ve3sjk/Cyclone-PCB-Factory/Output_files/1212m4/dev pics/2014-12-06 12.56.31.jpg

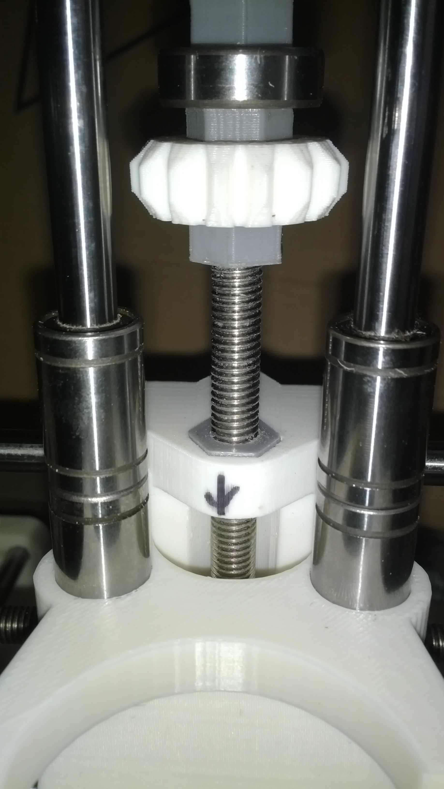
Output_files/1212m4/dev pics/2014-12-06 12.56.31.jpg
