ve3sjk/Cyclone-PCB-Factory/Output_files/1212m4/dev pics/2014-12-06 17.03.23.jpg

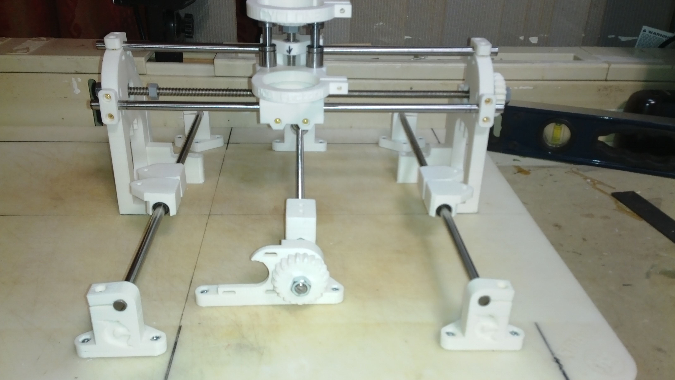
Output_files/1212m4/dev pics/2014-12-06 17.03.23.jpg
