ve3sjk/Cyclone-PCB-Factory/Output_files/ShorterVersion/Cyclone_XrightFrame.stl

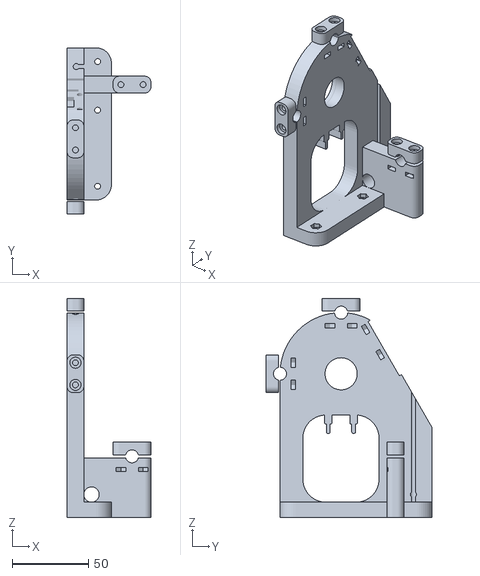
[picture p36: CAD file, 2014-12-10]
Output_files/ShorterVersion/Cyclone_XrightFrame.stl
54.9 x 108.8 x 143.2
