ve3sjk/Cyclone-PCB-Factory/Output_files/templates/Cyclone_workbed_template.dxf

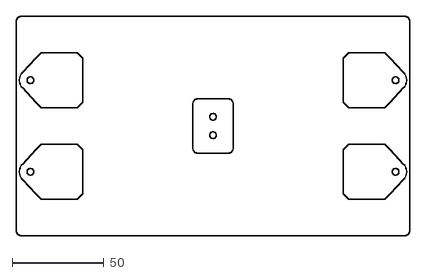
[picture p37: CAD file, 2014-12-10]
Output_files/templates/Cyclone_workbed_template.dxf
215.0 x 120.0
