ve3sjk/Cyclone-PCB-Factory/Output_files/templates/laserCut/Cyclone_workbed_8mm.dxf

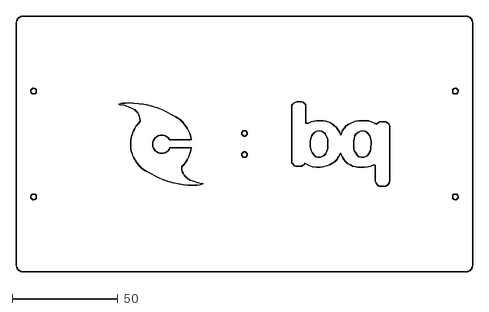
[picture p38: CAD file, 2014-12-10]
Output_files/templates/laserCut/Cyclone_workbed_8mm.dxf
216.0 x 121.0
