ve3sjk/Cyclone-PCB-Factory/Source_files/dxf/oshw.dxf

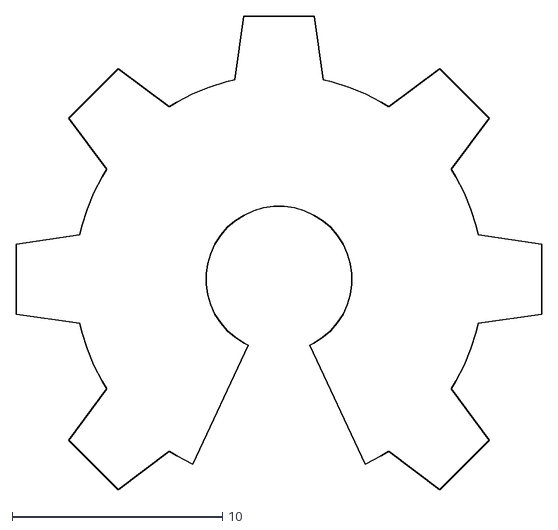
[picture p39: CAD file, 2014-12-10]
Source_files/dxf/oshw.dxf
25.0 x 22.5
