ve3sjk/Cyclone-PCB-Factory/Output_files/1212m4/stl/yleftidler.stl

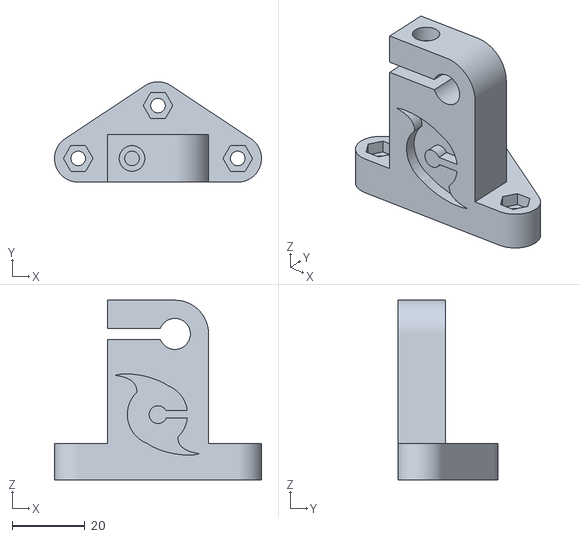
[picture p40: CAD file, 2014-12-08]
Output_files/1212m4/stl/yleftidler.stl
56.8 x 27.5 x 49.2
