ve3sjk/Cyclone-PCB-Factory/Output_files/1212m4/Tool Mounts/Dremel XPR-400 Mount/stl/btm.stl

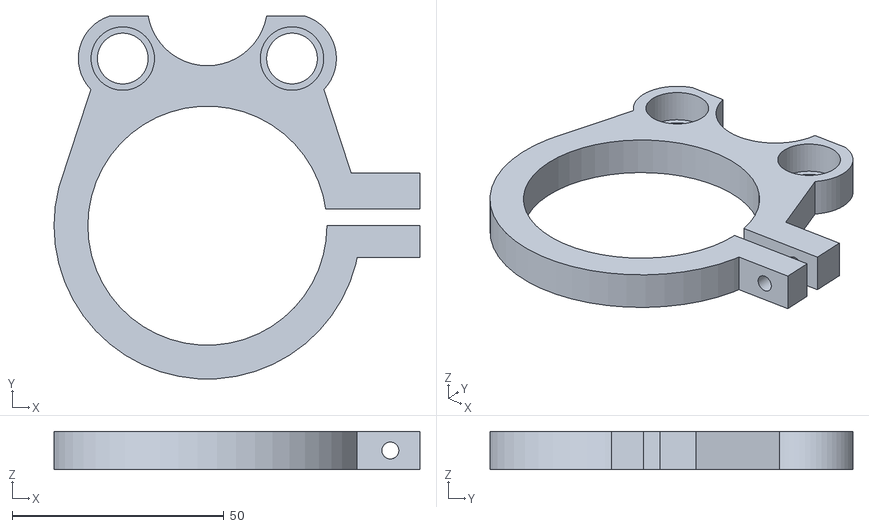
[picture p41: CAD file, 2014-12-08]
Output_files/1212m4/Tool Mounts/Dremel XPR-400 Mount/stl/btm.stl
86.5 x 85.7 x 9.00
