ve3sjk/Cyclone-PCB-Factory/Output_files/Cycl_YbackFrame.stl

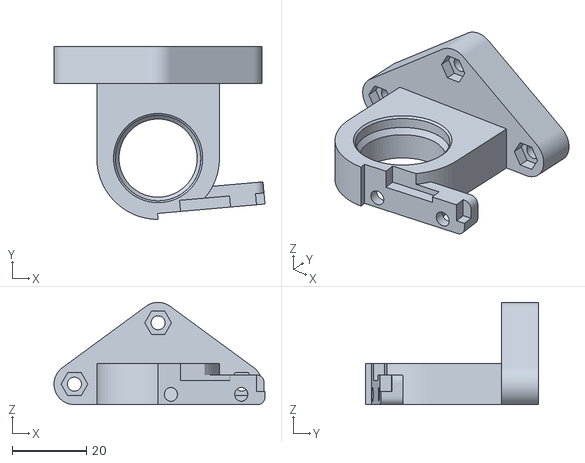
[picture p42: CAD file, 2014-12-10]
Output_files/Cycl_YbackFrame.stl
56.7 x 46.5 x 27.5
