ve3sjk/Cyclone-PCB-Factory/Output_files/templates/laserCut/Electrodo_Calibracion_Cyclone.dxf

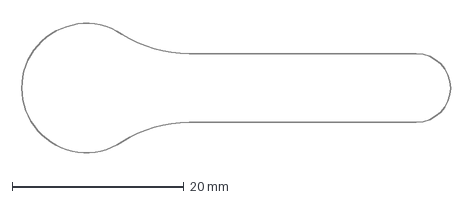
[picture p43: CAD file, 2014-12-10]
Output_files/templates/laserCut/Electrodo_Calibracion_Cyclone.dxf
50.6 x 16.7 mm
