ve3sjk/Cyclone-PCB-Factory/Output_files/1212m4/stl/ygearrod.stl

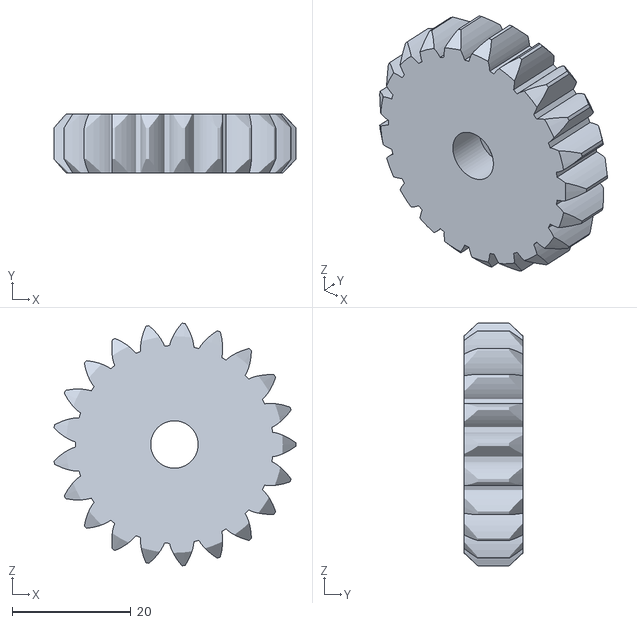
[picture p44: CAD file, 2014-12-08]
Output_files/1212m4/stl/ygearrod.stl
40.7 x 10.0 x 40.8
