ve3sjk/Cyclone-PCB-Factory/Output_files/templates/laserCut/Cyclone_Base_8mm.dxf

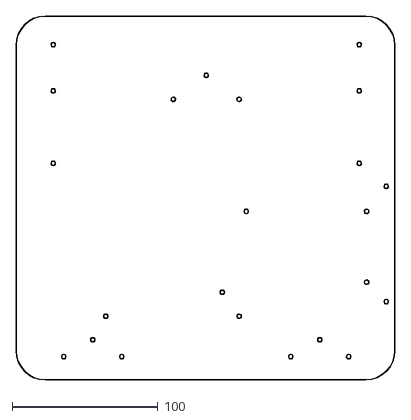
[picture p45: CAD file, 2014-12-10]
Output_files/templates/laserCut/Cyclone_Base_8mm.dxf
260.0 x 249.5
