ve3sjk/Cyclone-PCB-Factory/Output_files/1212m4/stl/yframefront.stl

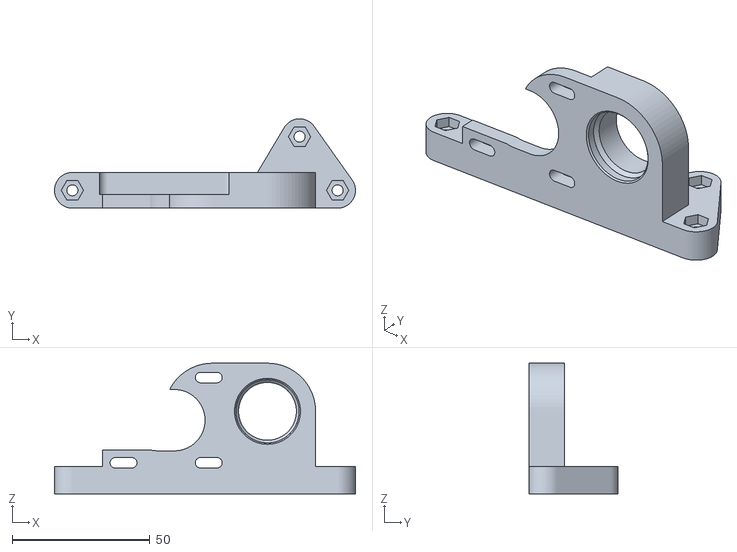
[picture p46: CAD file, 2014-12-08]
Output_files/1212m4/stl/yframefront.stl
109.5 x 32.5 x 47.5
