ve3sjk/Cyclone-PCB-Factory/Output_files/Cycl_Ycarriage_nutHolder.stl

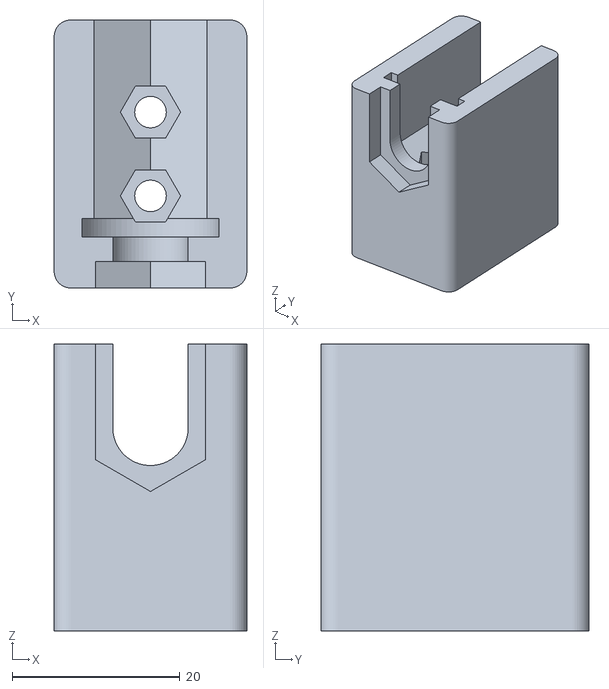
[picture p47: CAD file, 2014-12-10]
Output_files/Cycl_Ycarriage_nutHolder.stl
23.0 x 32.0 x 34.2
