ve3sjk/Cyclone-PCB-Factory/Output_files/1212m4/stl/ymotgear.stl

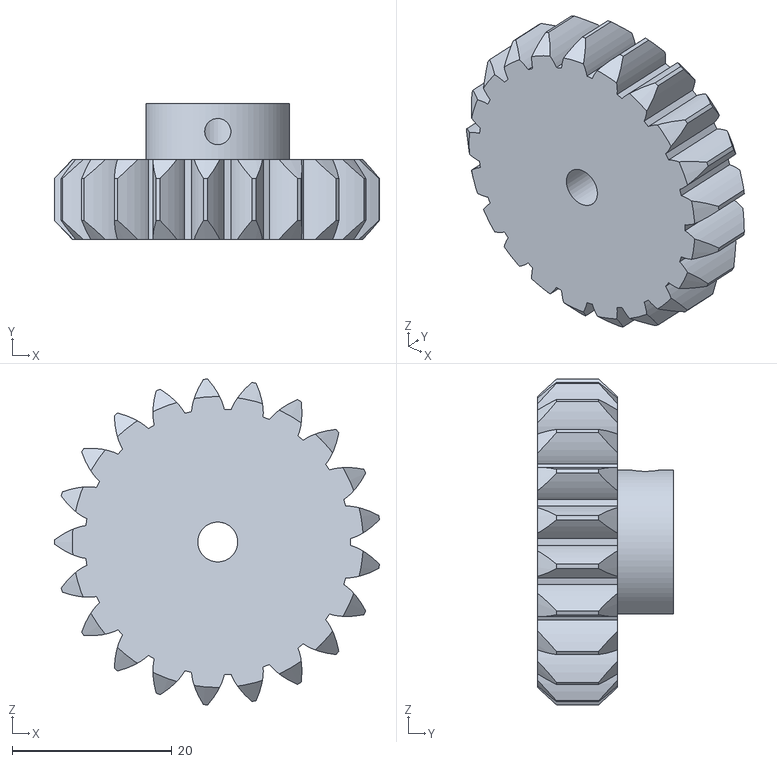
[picture p48: CAD file, 2014-12-08]
Output_files/1212m4/stl/ymotgear.stl
40.7 x 17.0 x 40.8
