ve3sjk/Cyclone-PCB-Factory/Output_files/Cycl_YfrontLeft_RodIdler.stl

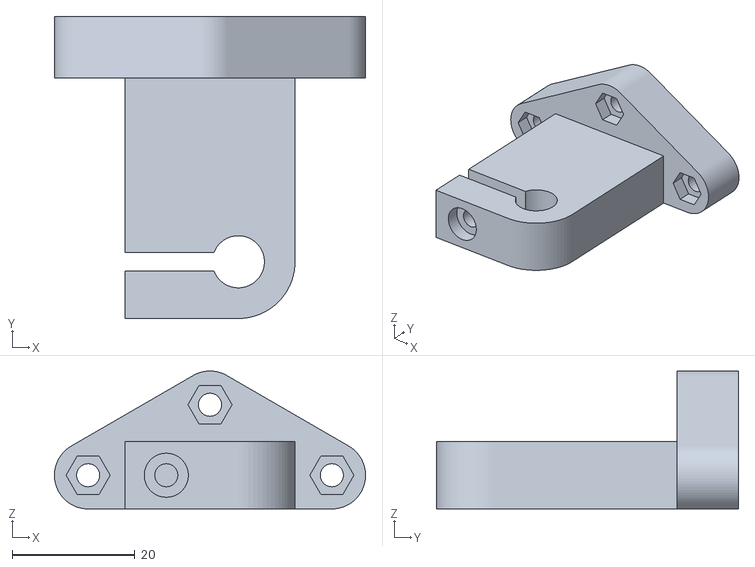
[picture p49: CAD file, 2014-12-10]
Output_files/Cycl_YfrontLeft_RodIdler.stl
50.8 x 49.2 x 22.5
