ve3sjk/Cyclone-PCB-Factory/Output_files/1212m4/stl/zcarraigetop.stl

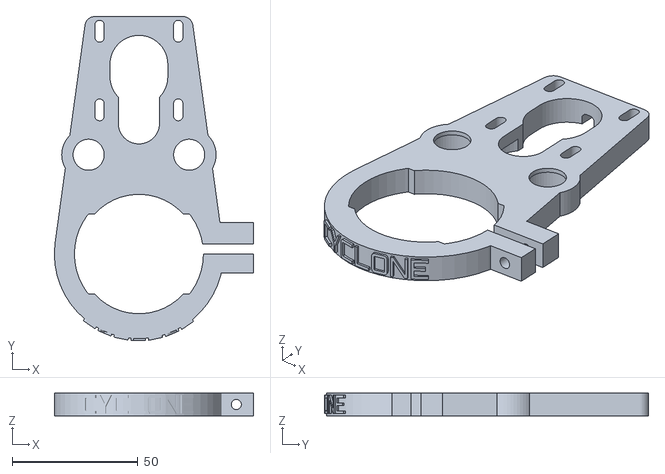
[picture p50: CAD file, 2014-12-08]
Output_files/1212m4/stl/zcarraigetop.stl
79.3 x 128.9 x 9.00
