ve3sjk/Cyclone-PCB-Factory/Output_files/Cycl_rodFixer_x6.stl

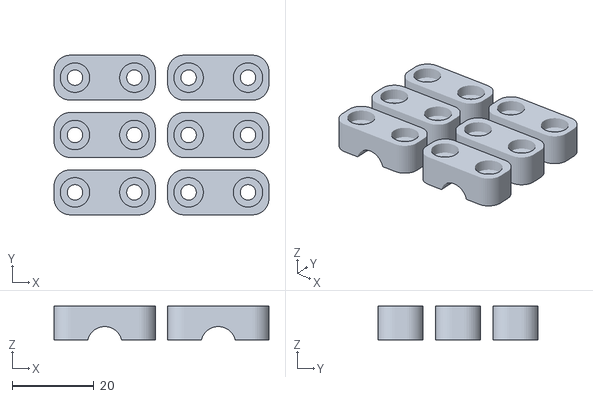
[picture p51: CAD file, 2014-12-10]
Output_files/Cycl_rodFixer_x6.stl
52.5 x 39.0 x 8.25
