ve3sjk/Cyclone-PCB-Factory/Output_files/Cycl_XYgearCover_x2.stl

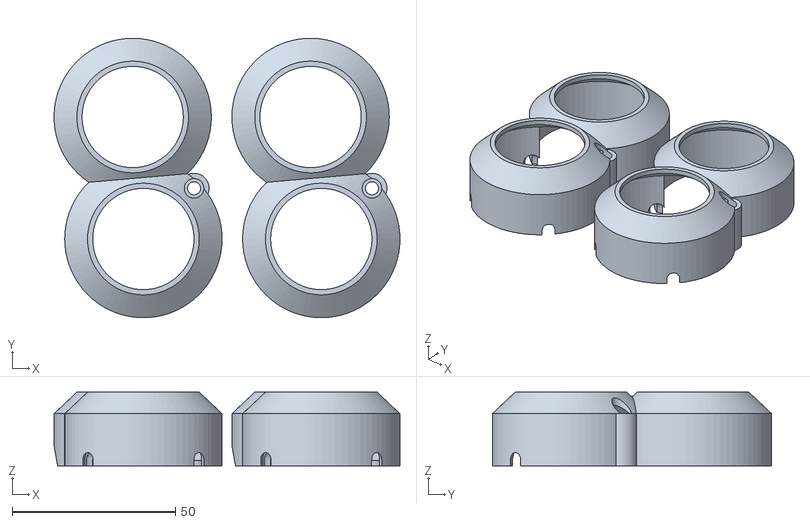
[picture p52: CAD file, 2014-12-10]
Output_files/Cycl_XYgearCover_x2.stl
105.9 x 85.6 x 22.6
