ve3sjk/Cyclone-PCB-Factory/Output_files/1212m4/stl/yframeback.stl

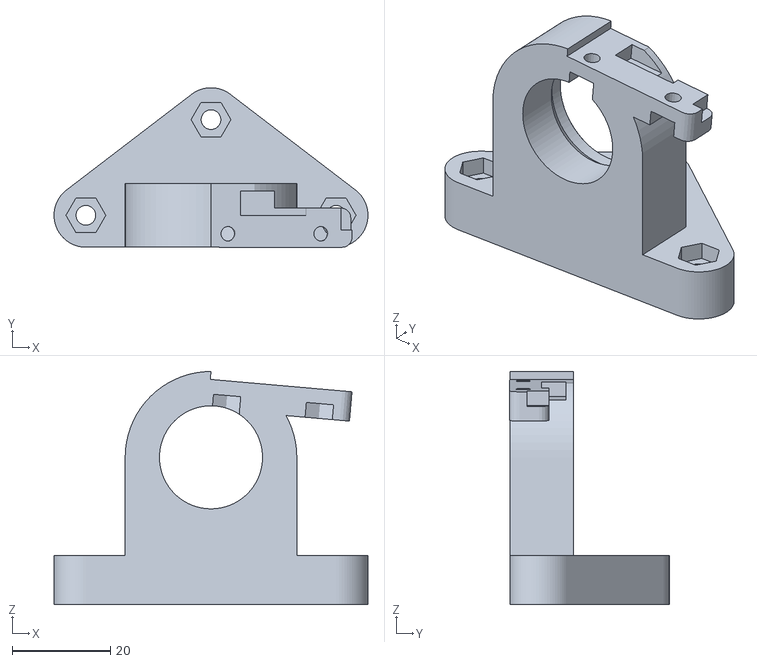
[picture p53: CAD file, 2014-12-08]
Output_files/1212m4/stl/yframeback.stl
64.0 x 32.5 x 47.5
