ve3sjk/Cyclone-PCB-Factory/Output_files/Cycl_allGears.stl

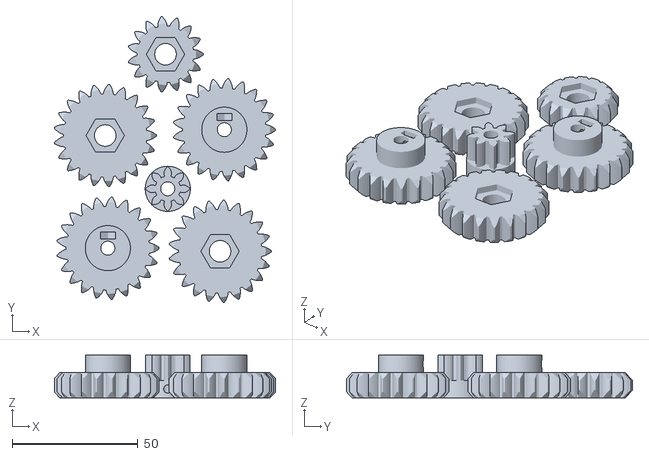
[picture p54: CAD file, 2014-12-10]
Output_files/Cycl_allGears.stl
88.2 x 113.9 x 17.0
