ve3sjk/Cyclone-PCB-Factory/Output_files/1212m4/stl/Ylm8uuHolder.stl

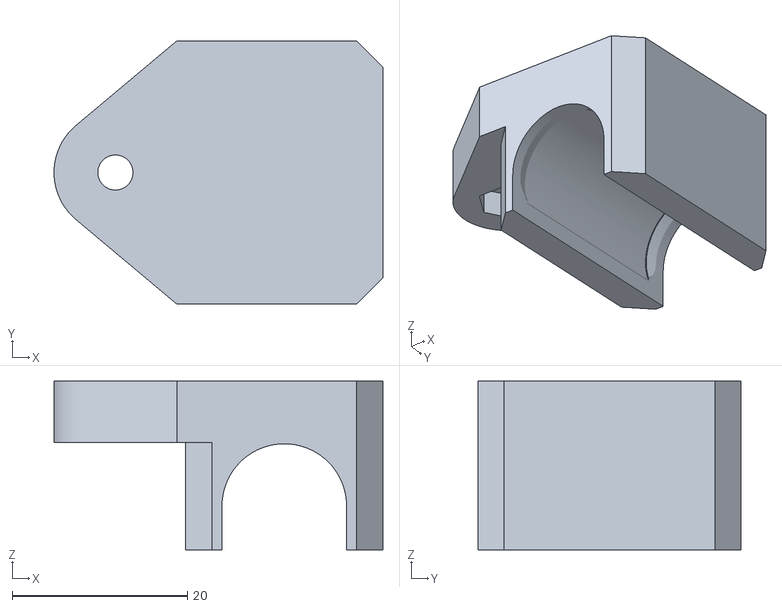
[picture p55: CAD file, 2014-12-08]
Output_files/1212m4/stl/Ylm8uuHolder.stl
37.5 x 30.0 x 19.3
