ve3sjk/Cyclone-PCB-Factory/Output_files/Cycl_XrightFrame.stl

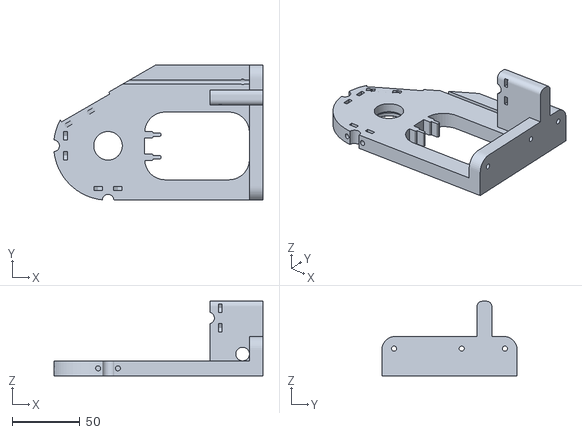
[picture p56: CAD file, 2014-12-10]
Output_files/Cycl_XrightFrame.stl
153.7 x 99.6 x 54.9
