ve3sjk/Cyclone-PCB-Factory/Output_files/Cycl_Zcarriage.stl

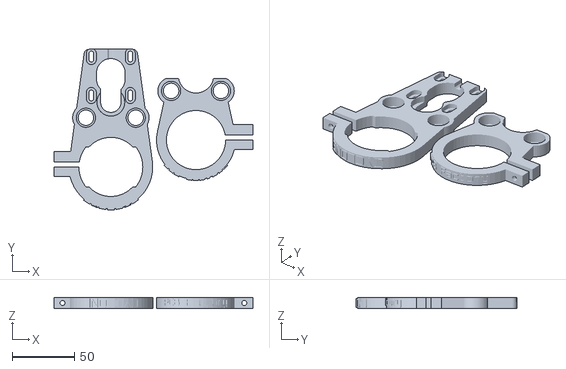
[picture p57: CAD file, 2014-12-10]
Output_files/Cycl_Zcarriage.stl
159.8 x 128.9 x 9.00
