ve3sjk/Cyclone-PCB-Factory/Output_files/Cycl_Ycarriage_PCBholder_x2.stl

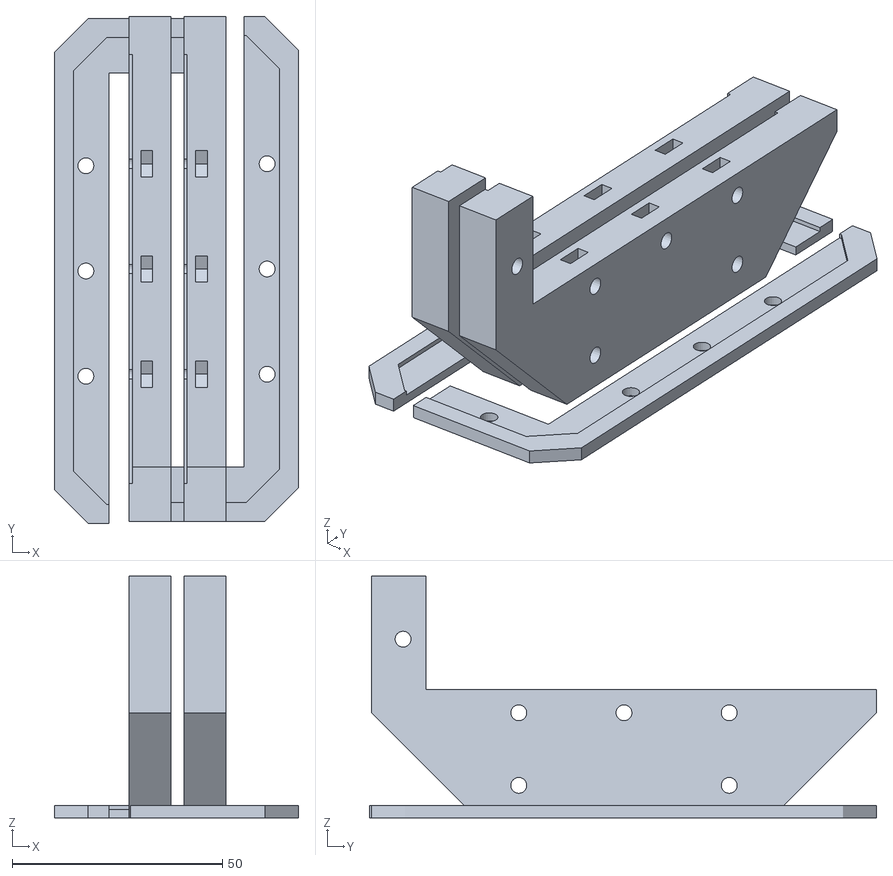
[picture p58: CAD file, 2014-12-10]
Output_files/Cycl_Ycarriage_PCBholder_x2.stl
58.1 x 120.5 x 57.5
