ve3sjk/Cyclone-PCB-Factory/Output_files/1212m4/stl/gearcover.stl

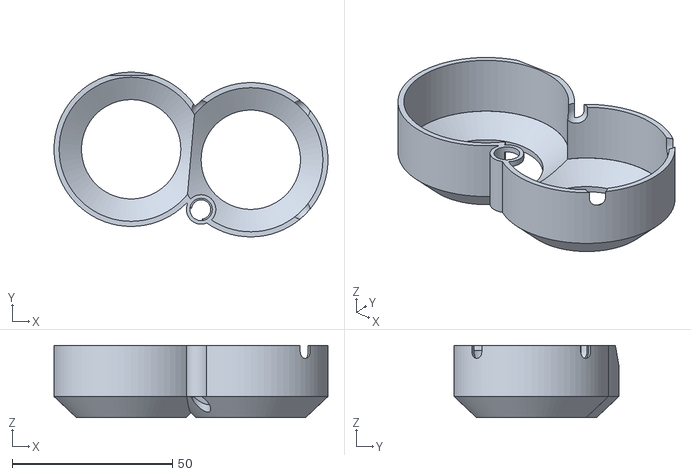
[picture p59: CAD file, 2014-12-08]
Output_files/1212m4/stl/gearcover.stl
85.6 x 51.5 x 22.6
