ve3sjk/Cyclone-PCB-Factory/Output_files/Cycl_vacuum_cleaner_attachment.stl

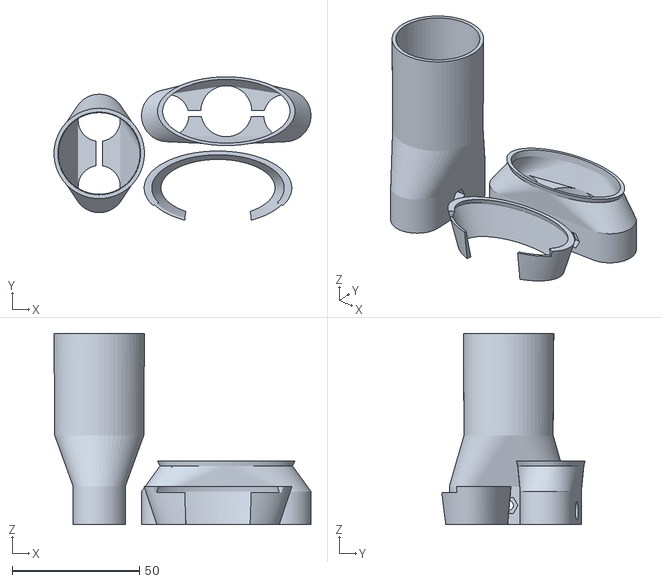
[picture p60: CAD file, 2014-12-10]
Output_files/Cycl_vacuum_cleaner_attachment.stl
100.9 x 56.3 x 75.0
