ve3sjk/Cyclone-PCB-Factory/Output_files/1212m4/stl/zcarraigebottom.stl

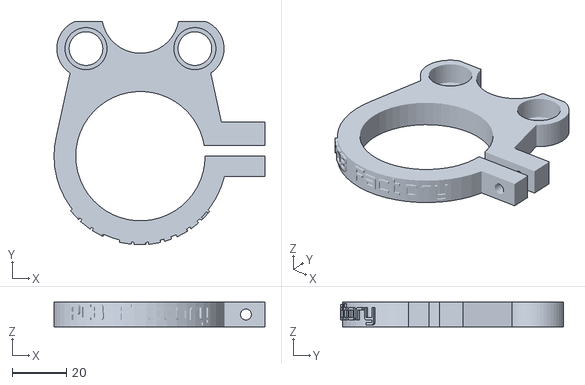
[picture p61: CAD file, 2014-12-08]
Output_files/1212m4/stl/zcarraigebottom.stl
77.5 x 82.0 x 9.00
