ve3sjk/Cyclone-PCB-Factory/Output_files/Cycl_Ycarriage_linearBearingHolder_x4.stl

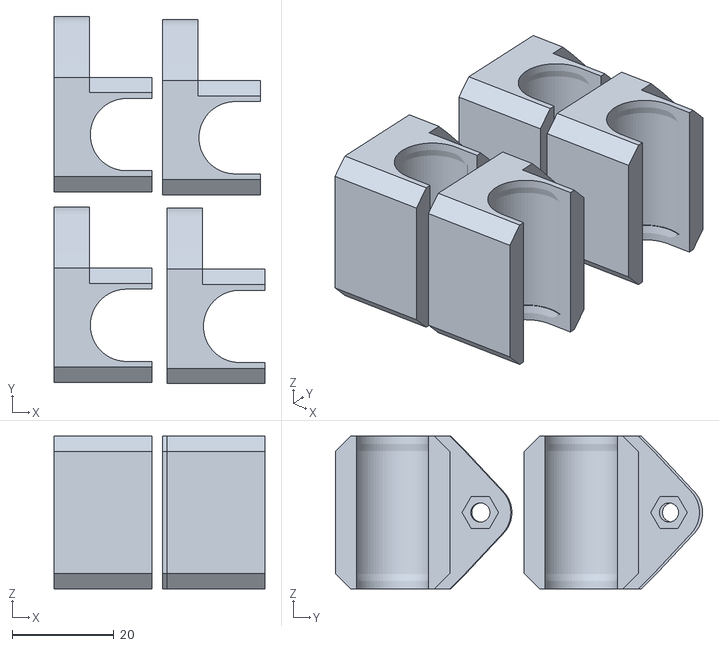
[picture p62: CAD file, 2014-12-10]
Output_files/Cycl_Ycarriage_linearBearingHolder_x4.stl
41.5 x 72.2 x 30.0
