ve3sjk/Cyclone-PCB-Factory/Output_files/1212m4/stl/xframeLeft.stl

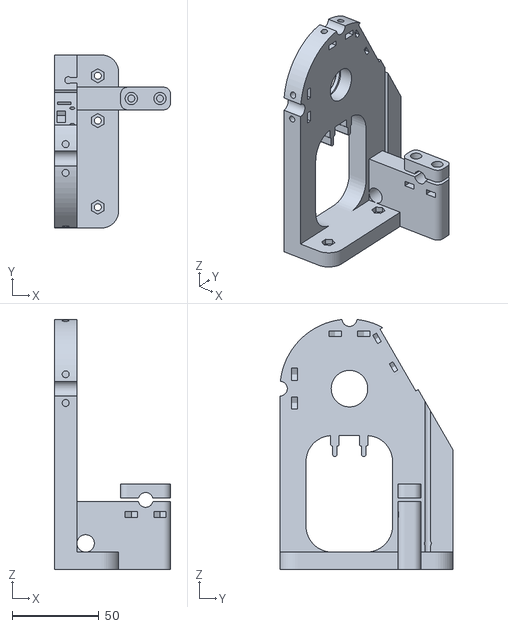
[picture p63: CAD file, 2014-12-08]
Output_files/1212m4/stl/xframeLeft.stl
66.9 x 99.6 x 143.7
