ve3sjk/Cyclone-PCB-Factory/Output_files/1212m4/stl/ynutholder.stl

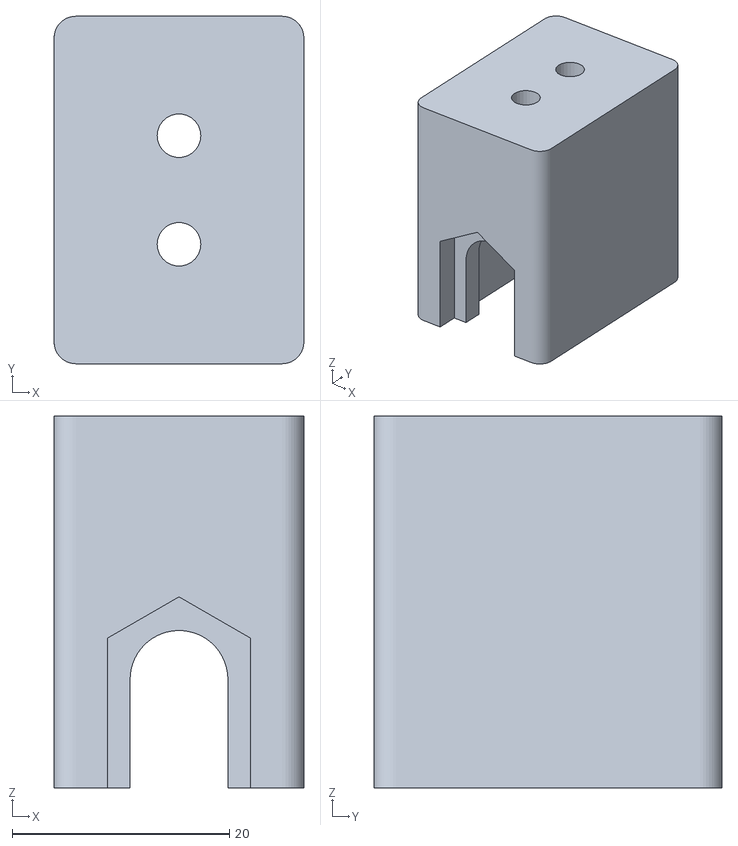
[picture p64: CAD file, 2014-12-08]
Output_files/1212m4/stl/ynutholder.stl
23.0 x 32.0 x 34.2
