ve3sjk/Cyclone-PCB-Factory/Output_files/1212m4/stl/smoothrodhold.stl

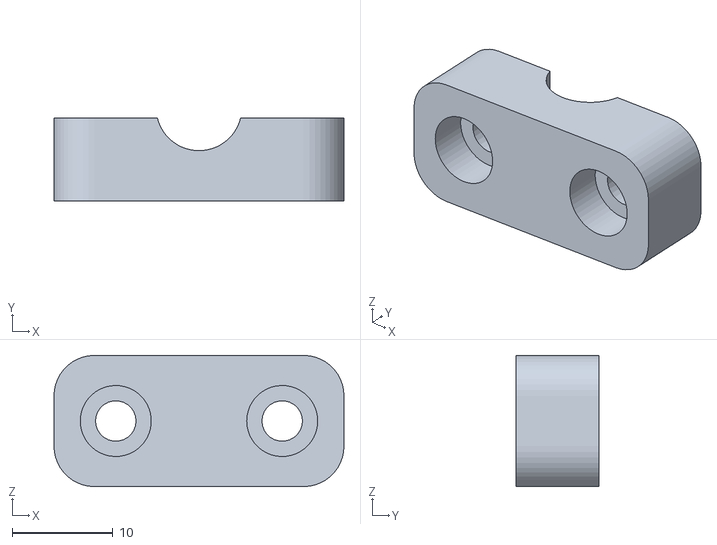
[picture p65: CAD file, 2014-12-08]
Output_files/1212m4/stl/smoothrodhold.stl
28.7 x 8.25 x 13.0
