ve3sjk/Cyclone-PCB-Factory/Firmware/MarlinForCyclone-Marlin_v1/ArduinoAddons/Arduino_0.xx/Gen7/cores/arduino/binary.h

#ifndef Binary_h
#define Binary_h

#define B0 0
#define B00 0
#define B000 0
#define B0000 0
#define B00000 0
#define B000000 0
#define B0000000 0
#define B00000000 0
#define B1 1
#define B01 1
#define B001 1
#define B0001 1
#define B00001 1
#define B000001 1
#define B0000001 1
#define B00000001 1
#define B10 2
#define B010 2
#define B0010 2
#define B00010 2
#define B000010 2
#define B0000010 2
#define B00000010 2
#define B11 3
#define B011 3
#define B0011 3
#define B00011 3
#define B000011 3
#define B0000011 3
#define B00000011 3
#define B100 4
#define B0100 4
#define B00100 4
#define B000100 4
#define B0000100 4
#define B00000100 4
#define B101 5
#define B0101 5
#define B00101 5
#define B000101 5
#define B0000101 5
#define B00000101 5
#define B110 6
#define B0110 6
#define B00110 6
#define B000110 6
#define B0000110 6
#define B00000110 6
#define B111 7
#define B0111 7
#define B00111 7
#define B000111 7
#define B0000111 7
#define B00000111 7
#define B1000 8
#define B01000 8
#define B001000 8
#define B0001000 8
#define B00001000 8
#define B1001 9
#define B01001 9
#define B001001 9
#define B0001001 9
#define B00001001 9
#define B1010 10
#define B01010 10
#define B001010 10
#define B0001010 10
#define B00001010 10
#define B1011 11
#define B01011 11
#define B001011 11
#define B0001011 11
#define B00001011 11
#define B1100 12
#define B01100 12
#define B001100 12
#define B0001100 12
#define B00001100 12
#define B1101 13
#define B01101 13
#define B001101 13
#define B0001101 13
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
#define B11110011 243
#define B11110100 244
#define B11110101 245
#define B11110110 246
#define B11110111 247
#define B11111000 248
#define B11111001 249
#define B11111010 250
#define B11111011 251
#define B11111100 252
#define B11111101 253
#define B11111110 254
#define B11111111 255

#endif
