ve3sjk/Cyclone-PCB-Factory/Firmware/MarlinForCyclone-Marlin_v1/ArduinoAddons/Arduino_1.x.x/hardware/Sanguino/cores/arduino/main.cpp

#include <Arduino.h>

int main(void)
{
	init();

#if defined(USBCON)
	USBDevice.attach();
#endif
	
	setup();
    
	for (;;) {
		loop();
		if (serialEventRun) serialEventRun();
	}
        
	return 0;
}
